giltesa/Andonstar-LED-Light/4. Photos/P1170249.jpg

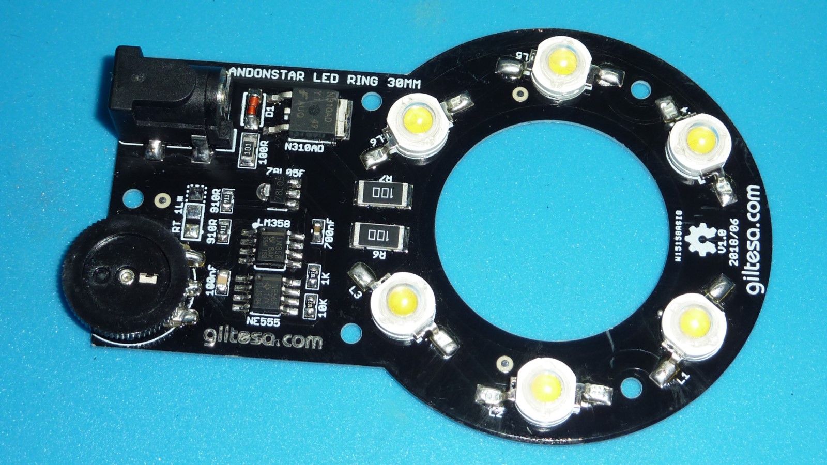
4. Photos/P1170249.jpg
