giltesa/Andonstar-LED-Light/4. Photos/P1170251.JPG

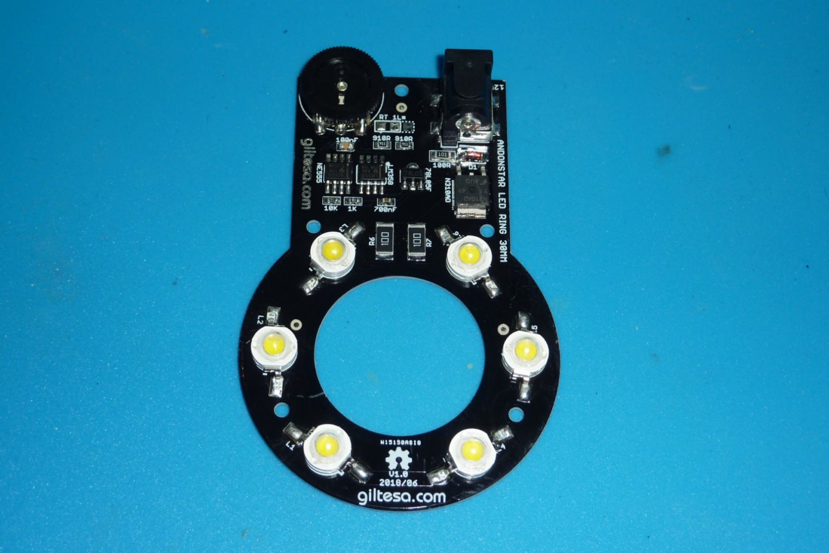
4. Photos/P1170251.JPG
