giltesa/Andonstar-LED-Light/4. Photos/P1170254.JPG

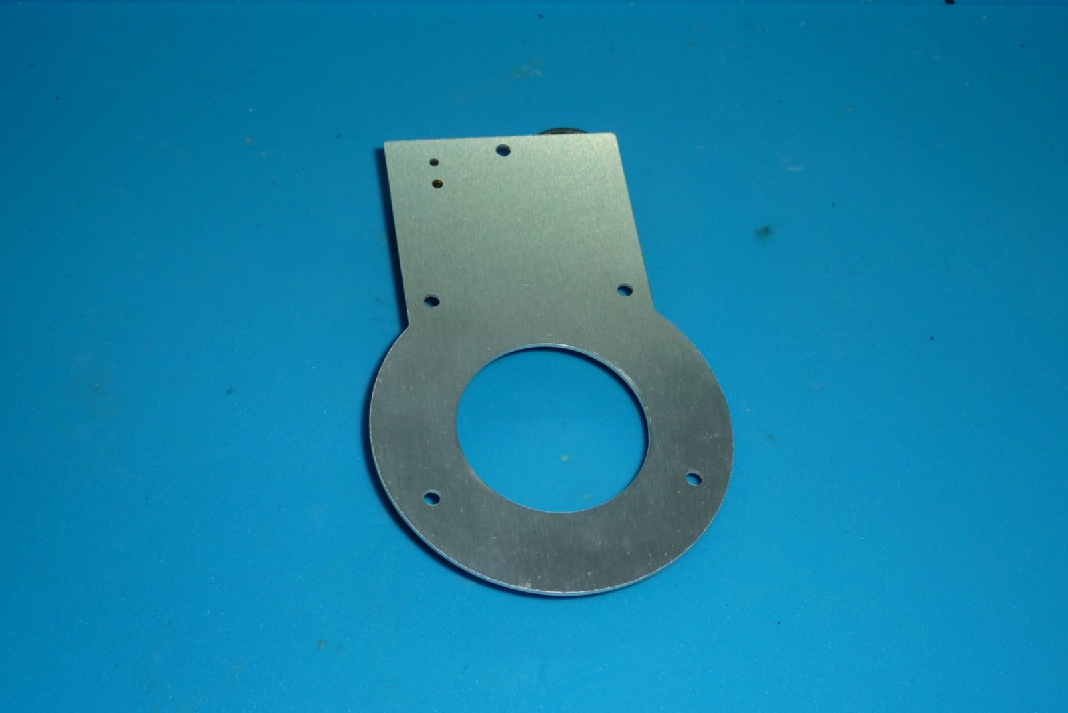
4. Photos/P1170254.JPG
